KacperParaniuk/MonARCH-Electrical-Payload/hw/PIB/monarch_payload_interface_board_rev2/EXLA1V0402-R82-R/EXLA.stp

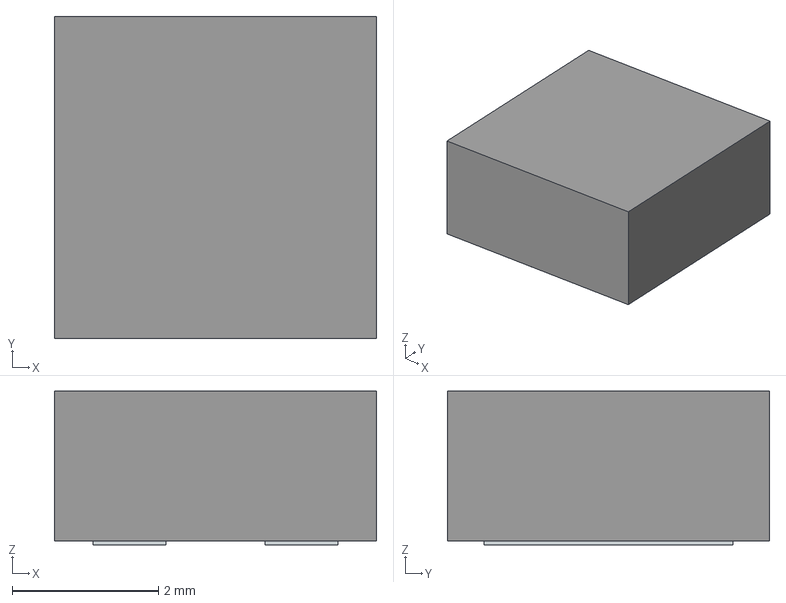
[picture p15: CAD file, 2026-03-08]
hw/PIB/monarch_payload_interface_board_rev2/EXLA1V0402-R82-R/EXLA.stp
4.40 x 4.40 x 2.10 mm
