KacperParaniuk/MonARCH-Electrical-Payload/hw/PIB/monarch_payload_interface_board_rev2/LIB_FZT600TA/FZT600TA/3D/FZT600TA.stp

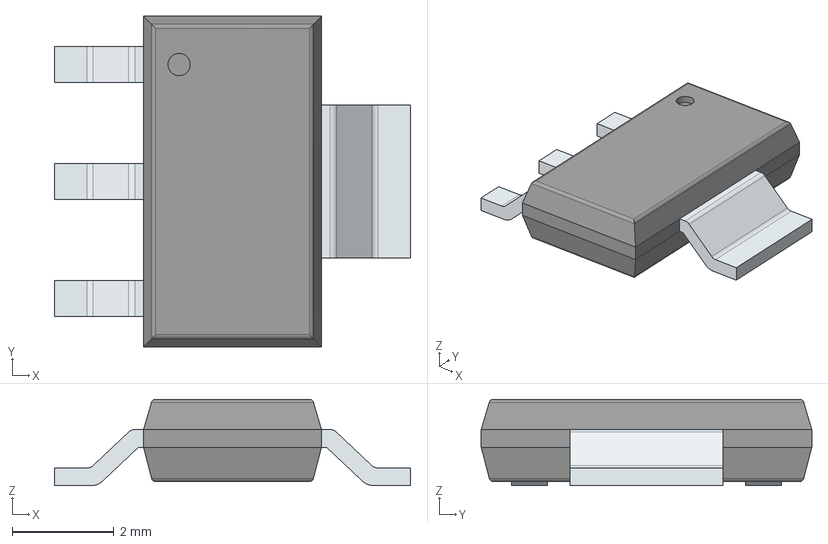
[picture p16: CAD file, 2026-02-22]
hw/PIB/monarch_payload_interface_board_rev2/LIB_FZT600TA/FZT600TA/3D/FZT600TA.stp
7.00 x 6.50 x 1.70 mm
PinsArrayL
FilletPinR
