KacperParaniuk/MonARCH-Electrical-Payload/hw/PIB/monarch_payload_interface_board_rev2/NZT7053/SOT-223_ONS.step

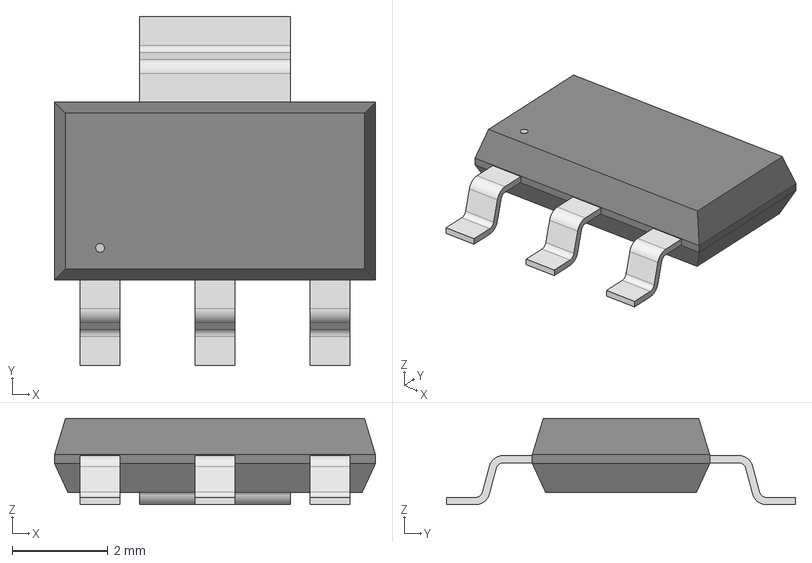
[picture p17: CAD file, 2026-02-22]
hw/PIB/monarch_payload_interface_board_rev2/NZT7053/SOT-223_ONS.step
6.71 x 7.29 x 1.81 mm
