KacperParaniuk/MonARCH-Electrical-Payload/hw/PIB/monarch_payload_interface_board_rev2/PIB_REV2.step

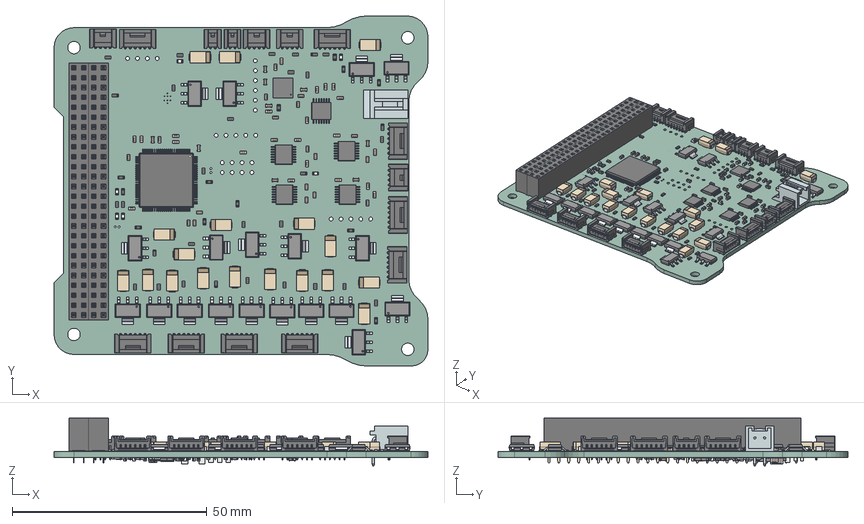
[picture p18: CAD file, 2026-07-30]
hw/PIB/monarch_payload_interface_board_rev2/PIB_REV2.step
96.0 x 89.9 x 12.3 mm
R_0603_1608Metric x 63
C_0603_1608Metric x 71
PinsArrayL x 19
FilletPinR x 19
LED_0603_1608Metric x 6
Body001 (Mirror #1) x 35
LQFP-100_14x14mm_P0.5mm
PinSocket_2x26_P2.54mm_Vertical x 2
534260210wbm000_01
WSK0612 x 3
C_1206_3216Metric x 2
C_0805_2012Metric x 5
BODY-QFN
PIN1-ID
monA6B6_PCB
