KacperParaniuk/MonARCH-Electrical-Payload/hw/PIB/monarch_payload_interface_board_rev2/S1J_13_F/SMA_DIO.step

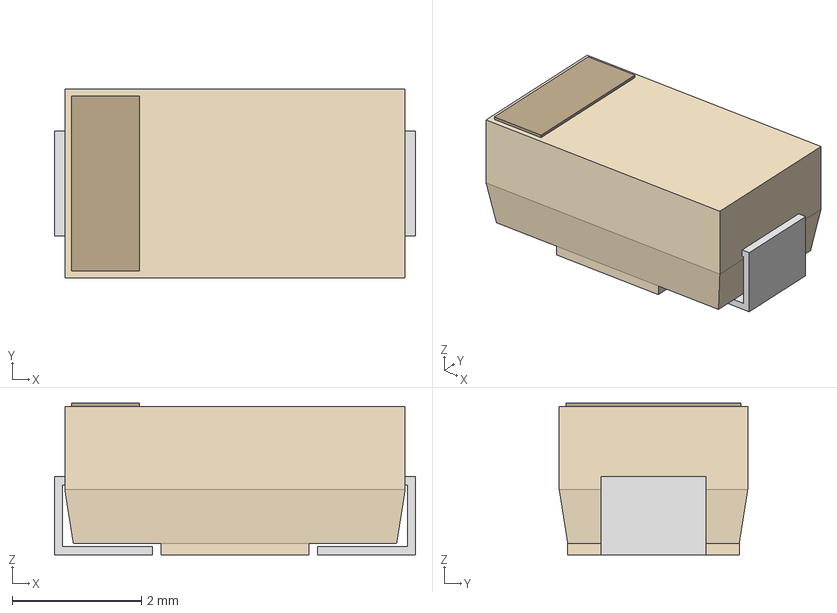
[picture p19: CAD file, 2026-02-22]
hw/PIB/monarch_payload_interface_board_rev2/S1J_13_F/SMA_DIO.step
5.59 x 2.92 x 2.35 mm
