KacperParaniuk/MonARCH-Electrical-Payload/hw/PIB/monarch_payload_interface_board_rev2/TPS61088QRHLRQ1/RHL0020A.stp

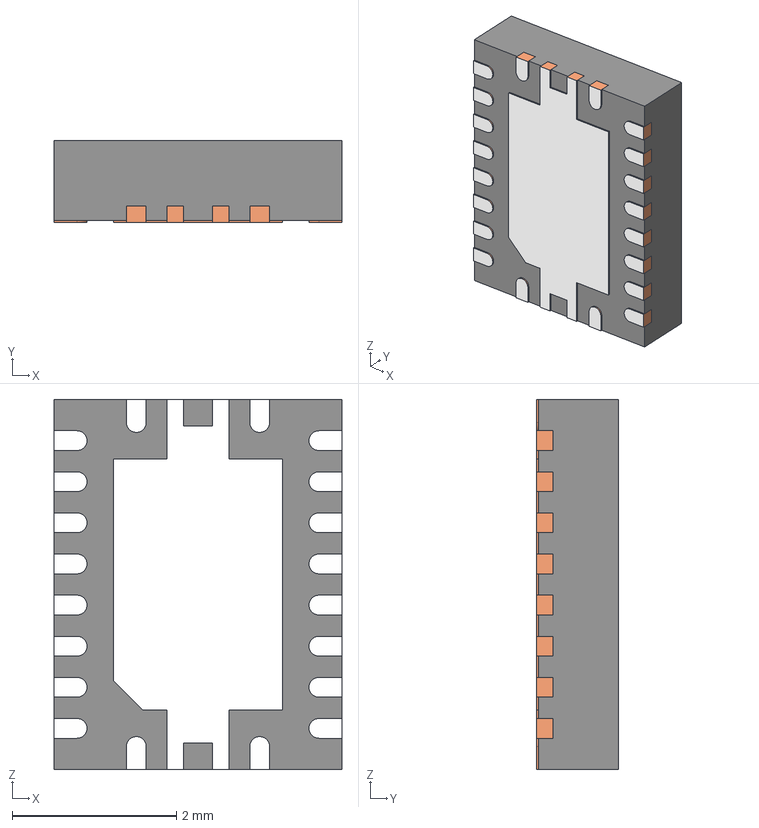
[picture p20: CAD file, 2026-02-22]
hw/PIB/monarch_payload_interface_board_rev2/TPS61088QRHLRQ1/RHL0020A.stp
3.50 x 1.00 x 4.50 mm
BODY-QFN
FRAME-RHL0020A
PIN1-ID
