KacperParaniuk/MonARCH-Electrical-Payload/hw/PIB/monarch_payload_interface_board_rev2/ul_WSK06121L000FEA/WSK0612.step

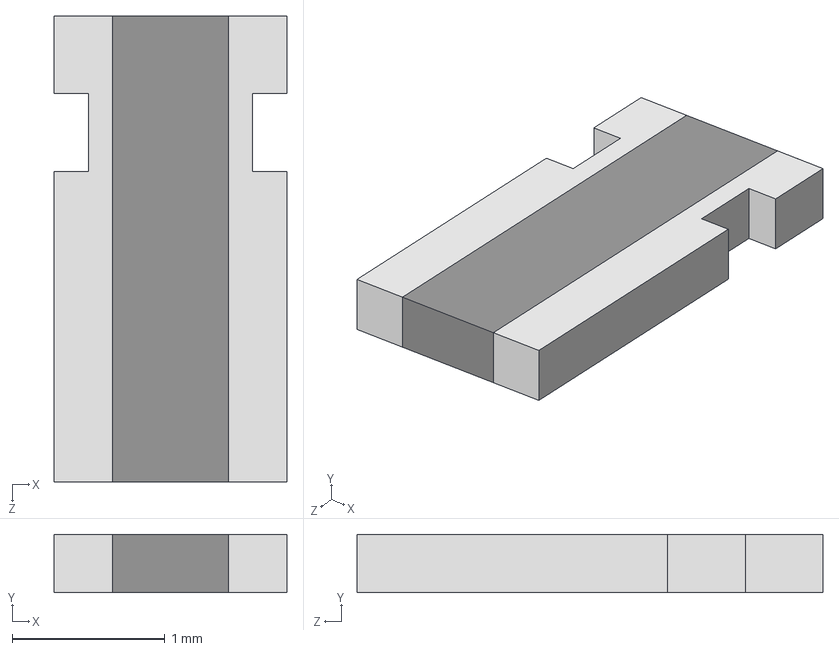
[picture p21: CAD file, 2026-03-08]
hw/PIB/monarch_payload_interface_board_rev2/ul_WSK06121L000FEA/WSK0612.step
1.52 x 0.381 x 3.05 mm
