KacperParaniuk/MonARCH-Electrical-Payload/sw/Main_PIB_Software/PIB_SOFTWARE/App/Inc/control_task.h

/*
 * contro_task.h
 *
 *  Created on: Mar 28, 2026
 *      Author: Kacper Paraniuk
 */

#ifndef INC_CONTROL_TASK_H_
#define INC_CONTROL_TASK_H_


#include "main.h"
#include <stdbool.h>
#include "max31856.h"


#define THRESHOLD_TEMP 60.0f // need to set correct threshold temperature value based on the readings we are getting.

void open_solenoid(GPIO_TypeDef* GPIO_port, uint16_t GPIO_Pin);
void close_solenoid(GPIO_TypeDef* GPIO_port, uint16_t GPIO_Pin);


int heat_catalyst(); // input a parameter into here to adjust the duty cycle of pwm signal. / the temperature




#endif /* INC_CONTROL_TASK_H_ */
