KacperParaniuk/MonARCH-Electrical-Payload/sw/Main_PIB_Software/PIB_SOFTWARE/BSP/Sensors/Inc/ad7124_sensor.h

/*
 * ad7124_sensor.h
 *
 *  Created on: Mar 17, 2026
 *      Author: Kacper Paraniuk
 */

#ifndef INC_AD7124_SENSOR_H_
#define INC_AD7124_SENSOR_H_


#include "ad7124.h"


extern struct ad7124_dev *ad7124;        // defined in main.c


#define CH_READ_PT0    0x0B
#define CH_READ_PT1    0x0C
#define CH_READ_PT2    0x0D
#define CH_READ_PT3    0x03
#define CH_READ_PT4    0x04
#define CH_READ_PT5    0x05
#define CH_READ_PT6    0x01
#define CH_READ_PT7    0x02


#define CH_READ_12VA_VB 0x00
#define CH_READ_12VA_VA 0x01
#define CH_READ_3V3_VB 0x02
#define CH_READ_3V3_VA 0x03
#define CH_READ_VBAT_VA 0x04
#define CH_READ_VBAT_VB 0x05
#define CH_READ_12VB_VA 0x06
#define CH_READ_12VB_VB 0x07


// Read a specific channel voltage
float ad7124_read_channel_voltage(struct ad7124_dev *device, uint8_t channel);
float ad7124_read_channel_current_pc104(struct ad7124_dev *device, uint8_t channel);




#endif /* INC_AD7124_SENSOR_H_ */
