KacperParaniuk/MonARCH-Electrical-Payload/sw/Main_PIB_Software/PIB_SOFTWARE/BSP/Sensors/Src/ad7124_console_app.c

/*!
 *****************************************************************************
  @file:  ad7124_console_app.c

  @brief: Implementation for the menu functions that handle the AD7124

  @details:
 -----------------------------------------------------------------------------
Copyright (c) 2019 Analog Devices, Inc.  All rights reserved.

Redistribution and use in source and binary forms, with or without modification,
are permitted provided that the following conditions are met:
  - Redistributions of source code must retain the above copyright notice,
    this list of conditions and the following disclaimer.
  - Redistributions in binary form must reproduce the above copyright notice,
    this list of conditions and the following disclaimer in the documentation
	and/or other materials provided with the distribution.
  - Modified versions of the software must be conspicuously marked as such.
  - This software is licensed solely and exclusively for use with processors/
    products manufactured by or for Analog Devices, Inc.
  - This software may not be combined or merged with other code in any manner
    that would cause the software to become subject to terms and conditions
	which differ from those listed here.
  - Neither the name of Analog Devices, Inc. nor the names of its contributors
    may be used to endorse or promote products derived from this software without
    specific prior written permission.
  - The use of this software may or may not infringe the patent rights of one
    or more patent holders.  This license does not release you from the
	requirement that you obtain separate licenses from these patent holders
	to use this software.

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
20180927-7CBSD SLA

*****************************************************************************/

/* includes */
#include <stdio.h>
#include <string.h>
#include <stdbool.h>

#include "platform_support.h"
#include "spi.h"
#include "error.h"

#include "ad7124.h"
#include "ad7124_regs.h"
#include "ad7124_support.h"
#include "ad7124_regs_configs.h"

#include "ad7124_console_app.h"


/*  defines */
#define AD7124_CHANNEL_COUNT 16

#define SHOW_ALL_CHANNELS     false
#define SHOW_ENABLED_CHANNELS  true

#define DISPLAY_DATA_TABULAR    0
#define DISPLAY_DATA_STREAM     1

#define MENU_ESCAPED			-1
#define MENU_CONTINUE           0
#define MENU_DONE               1

/* Private Variables */
/*
 * This is the 'live' AD7124 register map that is used by the driver
 * the other 'default' configs are used to populate this at init time
 */
static struct ad7124_st_reg ad7124_register_map_p[AD7124_REG_NO];

static struct ad7124_st_reg ad7124_register_map_v[AD7124_REG_NO];


// Pointer to the struct representing the AD7124 device // need to be able to utilize two ad7124 devices.

static struct ad7124_dev * pAd7124_dev = NULL; // p for pressure

// --------------

static struct ad7124_dev * vAd7124_dev = NULL; // v for voltage

uint32_t status;

// Last Sampled values for All ADC channels
static uint32_t channel_samples[AD7124_CHANNEL_COUNT] = {0};
// How many times a given channel is sampled in total for one sample run
static uint32_t channel_samples_count[AD7124_CHANNEL_COUNT] = {0};

// MAY USE THESE WHEN INTEGRATING DRIVER FUNCTIONS INTO MAIN.C

// Public Functions

/*!
 * @brief      Initialize the AD7124 device and the SPI port as required
 *
 * @details    This resets and then writes the default register map value to
 *  		   the device.  A call to init the SPI port is made, but may not
 *  		   actually do very much, depending on the platform
 */
int32_t ad7124_app_initialize(uint8_t configID, AD7124_CHIP chip)

// added param for cs -> CS = 0 = AD7124 POWER      |
				//       CS = 1 = AD7124 PRESSURE   | for measuring
{
	/*
	 * Copy one of the default/user configs to the live register memory map
	 * Requirement, not checked here, is that all the configs are the same size
	 *
	 */



	struct ad7124_st_reg *target_map = (chip == PRESSURE) ? ad7124_register_map_p : ad7124_register_map_v;

	switch(configID) {
		case AD7124_CONFIG_A:
		{
			memcpy(target_map, ad7124_regs_config_a, sizeof(struct ad7124_st_reg) * AD7124_REG_NO);
			break;
		}
		case AD7124_CONFIG_B:
		{
			memcpy(target_map, ad7124_regs_config_b, sizeof(struct ad7124_st_reg) * AD7124_REG_NO);
			break;
		}
		default:
			// Not a defined configID
			return(FAILURE);
	}




	if(chip==PRESSURE){

		// Used to create the ad7124 device (pressure)
	    struct	ad7124_init_param sAd7124_init = // ensure that when you are setting modfe
	  	{
	  		// spi_init_param type
	  		{
	  			2500000, 		// Max SPI Speed
	  			chip,				// Chip Select
				SPI_MODE_3,		// CPOL = 1, CPHA =1
				NULL
	  		},
	  		ad7124_register_map_p,

	  		10000				// Retry count for polling
	  	};

	    return(ad7124_setup(&pAd7124_dev, sAd7124_init));

	}

	else if(chip == VOLTAGE){

		// Used to create the ad7124 device (voltage)
	    struct	ad7124_init_param svAd7124_init = // ensure that when you are setting modfe
	  	{
	  		// spi_init_param type
	  		{
	  			2500000, 		// Max SPI Speed
	  			chip,				// Chip Select
				SPI_MODE_3,		// CPOL = 1, CPHA =1
				NULL

	  		},
	  		ad7124_register_map_v,

	  		10000				// Retry count for polling
	  	};


	    return(ad7124_setup(&vAd7124_dev, svAd7124_init));


	}

	return -20;

}


// ----- NOT USING MENU ------



// Private Functions

/*!
 * @brief      determines if the Escape key was pressed
 *
 * @details
 */
//static bool was_escape_key_pressed(void)
//{
//	char rxChar;
//	bool wasPressed = false;
//
//	// Check for Escape key pressed
//	if ((rxChar = getchar_nonblocking()) > 0) {
//		if (rxChar == ESCAPE_KEY_CODE) {
//			wasPressed = true;
//		}
//	}
//	return (wasPressed);
//}


/*!
 * @brief      reads and displays the status register on the AD7124
 *
 * @details
 */
void read_status_register(AD7124_CHIP chip)
{

    struct ad7124_dev *dev = (chip == PRESSURE) ? pAd7124_dev : vAd7124_dev;

	status = ad7124_read_register(dev, &dev->regs[AD7124_Status]);

	if (status < 0) {
	   printf("\r\nError Encountered reading Status register\r\n");
	} else {
	    uint32_t status_value = (uint32_t)dev->regs[AD7124_Status].value;
       printf("\r\nRead Status Register = 0x%02lx\r\n", status_value);
	}
}

static uint32_t error_value = 0;



void read_error_register(AD7124_CHIP chip){


    struct ad7124_dev *dev = (chip == PRESSURE) ? pAd7124_dev : vAd7124_dev;

	if (ad7124_read_register(dev, &dev->regs[AD7124_Error])==0){
		error_value = (uint32_t)dev->regs[AD7124_Error].value;
		if((error_value & AD7124_ERR_REG_ROM_CRC_ERR) != 0){
			printf("\r\n ROM Contents changed: CRC calculation fail: ROM error. \n");
		}
		if((error_value & AD7124_ERR_REG_MM_CRC_ERR) != 0){
			printf("\r\n CRC proves memory map changed: Memory map error. \n");
		}
		if((error_value & AD7124_ERR_REG_SPI_CRC_ERR) != 0){
			printf("\r\n CRC proves SPI read/write failed \n");
		}
		if((error_value & AD7124_ERR_REG_SPI_WRITE_ERR) != 0){
			printf("\r\n SPI write operation failed:  write to invalid addresses or write to read-only registers \n");
		}
		if((error_value & AD7124_ERR_REG_SPI_READ_ERR) != 0){
			printf("\r\n SPI read operation failed: attempt to read from invalid addresses \n");
		}
		if((error_value & AD7124_ERR_REG_SPI_SLCK_CNT_ERR) != 0){
			printf("\r\n The SCLK counter is enabled. All read and write operations to the ADC are multiples of eight bits: SCLK pulses used during a communication were not a multiple of eight \n");
		}
		if((error_value & AD7124_ERR_REG_SPI_IGNORE_ERR) != 0){
			printf("\r\n write operations are ignored from on chip registers ADC is busy and the write instruction has been ignored \n");
		}
		if((error_value & AD7124_ERR_REG_ALDO_PSM_ERR) != 0){
			printf("\r\n analog ldo: voltage being output from the analog LDO is outside specification. \n");
		}
		if((error_value & AD7124_ERR_REG_DLDO_PSM_ERR) != 0){
			printf("\r\n digital ldo: input to the test circuit is tied to DGND instead of the LDO output \n");
		}
		if((error_value & AD7124_ERR_REG_REF_DET_ERR) != 0){
			printf("\r\n External reference is an open circuit or has a value of less than 0.7 V. \n");
		}
		if((error_value & AD7124_ERR_REG_AINM_UV_ERR) != 0){
			printf("\r\n Undervoltage detection on AINM. \n");
		}
		if((error_value & AD7124_ERR_REG_AINM_OV_ERR) != 0){
			printf("\r\n Overvoltage detection on AINM. \n");
		}
		if((error_value & AD7124_ERR_REG_AINP_UV_ERR) != 0){
			printf("\r\n Undervoltage detection on AINP. \n");
		}
		if((error_value & AD7124_ERR_REG_AINP_OV_ERR) != 0){
			printf("\r\n Overvoltage detection on AINP \n");
		}
		if((error_value & AD7124_ERR_REG_ADC_SAT_ERR) != 0){
			printf("\r\n ADC saturation flag. This flag is set if the modulator is saturated during a conversion. \n");
		}
		if((error_value & AD7124_ERR_REG_ADC_CONV_ERR) != 0){
			printf("\r\n error occured during a conversion.");
		}
		if((error_value & AD7124_ERR_REG_ADC_CAL_ERR) != 0){
			printf("\r\n calibration error");
		}
		if((error_value & AD7124_ERR_REG_LDO_CAP_ERR) != 0){
			printf("\r\n decoupling capacitors required for the analog and digital LDOs are not connected to the AD7124-8.");
		}
	}
	else{
		printf("\r\n Error reading error register \n");
	}

}



/*!
 * @brief      displays the current sample value for a ADC channels
 *
 * @details
 *
 * @param showOnlyEnabledChannels  only channels that are enabled are displayed
 *
 */
static void dislay_channel_samples(bool showOnlyEnabledChannels, uint8_t console_mode, AD7124_CHIP chip)
{

    struct ad7124_dev *dev = (chip == PRESSURE) ? pAd7124_dev : vAd7124_dev;

	switch(console_mode) {
		case DISPLAY_DATA_TABULAR:
		{
			printf("\tCh\tValue\t\tCount\t\tVoltage\r\n");
			for (uint8_t i = 0; i < AD7124_CHANNEL_COUNT; i++) {
				// if showing all channels, or channel is enabled
				if ((showOnlyEnabledChannels == false) || (dev->regs[AD7124_Channel_0 + i].value & AD7124_CH_MAP_REG_CH_ENABLE) ) {
				   printf("\t%-2d\t%-10ld\t%ld\t\t% .6f\r\n",
							i, channel_samples[i], channel_samples_count[i],
							ad7124_convert_sample_to_voltage(dev, i, channel_samples[i]) );
				}
			}
			break;
		}
		case DISPLAY_DATA_STREAM:
		{
			// Output a CSV list of the sampled channels as voltages on a single line
			bool channel_printed = false;

			for (uint8_t i = 0; i < AD7124_CHANNEL_COUNT; i++) {
				// if showing all channels, or channel is enabled
				if ((showOnlyEnabledChannels == false) || (dev->regs[AD7124_Channel_0 + i].value & AD7124_CH_MAP_REG_CH_ENABLE) ) {
					/*
					 *  add the comma before we output the next channel but
					 *  only if at least one channel has been printed
					 */
				   if (channel_printed) {
					   printf(", ");
				   }
					printf("%.6f",
							ad7124_convert_sample_to_voltage(dev, i, channel_samples[i]) );
					channel_printed = true;
				}
			}
			printf("\r\n");
			break;
		}
		default:
		{
			// ASSERT(false);
		}
	}
}


float display_channel_sample(uint8_t channel, AD7124_CHIP chip){
	float value;

    struct ad7124_dev *dev = (chip == PRESSURE) ? pAd7124_dev : vAd7124_dev;

	// sample data into array
	menu_single_conversion(chip);


	// print channel
	value = ad7124_convert_sample_to_voltage(dev, channel, channel_samples[channel]);
	return value;
		//	printf("Channel %d: Voltage: %f ",channel, value);

}


/*!
 * @brief      resets the channelSampleCounts to zero
 *
 * @details
 */
static void clear_channel_samples(void)
{
    for (uint8_t i = 0; i < AD7124_CHANNEL_COUNT; i++) {
    	channel_samples[i] = 0;
    	channel_samples_count[i] = 0;
    }
}


/*!
 * @brief      Continuously acquires samples in Continuous Conversion mode
 *
 * @details   The ADC is run in continuous mode, and all samples are acquired
 *            and assigned to the channel they come from. Escape key an be used
 *            to exit the loop
 */
//
int32_t do_continuous_conversion(uint8_t display_mode,  AD7124_CHIP chip)
//
//
//  THOUGHTS ON CONTINOUS CONVERSION
//
//  IF I RUN THIS function in code it should just loop forever. And later I want to have a command that can toggle this on / off. Or just avoid function completely and only sample on command rather than continously
//
//
//
{
    struct ad7124_dev *dev = (chip == PRESSURE) ? pAd7124_dev : vAd7124_dev;

	int32_t error_code;
	int32_t sample_data;

	// Clear the ADC CTRL MODE bits, has the effect of selecting continuous mode
    dev->regs[AD7124_ADC_Control].value &= ~(AD7124_ADC_CTRL_REG_MODE(0xf));
	if ( (error_code = ad7124_write_register(dev, dev->regs[AD7124_ADC_Control]) ) < 0) {
		printf("Error (%ld) setting AD7124 Continuous conversion mode.\r\n", error_code);


//		adi_press_any_key_to_continue();
		return(MENU_CONTINUE);

	}

	clear_channel_samples();

	/*
	 *  If displaying data in stream form, want to output a channel header
	 */
	if (display_mode == DISPLAY_DATA_STREAM)
	{
		bool channel_printed = false;

		for (uint8_t i = 0; i < AD7124_CHANNEL_COUNT; i++) {
		   // if showing all channels, or channel is enabled
			if (dev->regs[AD7124_Channel_0 + i].value & AD7124_CH_MAP_REG_CH_ENABLE) {
				/*
				 *  add the comma before we output the next channel but
				 *  only if at least one channel has been printed
				 */
			   if (channel_printed) {
				   printf(", ");
			   }
				printf("%d", i);
			}
			channel_printed = true;
		}
		printf("\r\n");
	}

	uint8_t loop = 0;

	// Continuously read the channels, and store sample values
    while (true) { // was_escape_key_pressed() != true
    	toggle_activity_led(); // BLUE LED THAT WILL INDICATE PROGRESS or that the chip is running in continous mode.


    	if (display_mode == DISPLAY_DATA_TABULAR) {
//    		adi_clear_console();
    		printf("Running continuous conversion mode...\r\nPress Escape to stop\r\n\r\n"); //
    		//
    		//   THIS IS WHERE THE COMMAND WOULD GO FOR STOPPING CONTINOUS MODE. CURRENTLY IT'S JUST STUCK IN IT
    		//
    		//
    		//
    	}

		/*
		 *  this polls the status register READY/ bit to determine when conversion is done
		 *  this also ensures the STATUS register value is up to date and contains the
		 *  channel that was sampled as well.
		 *  Generally, no need to read STATUS separately, but for faster sampling
		 *  enabling the DATA_STATUS bit means that status is appended to ADC data read
		 *  so the channel being sampled is read back (and updated) as part of the same frame
		 */

    	if ( (error_code = ad7124_wait_for_conv_ready(dev, 10000)) < 0) {
    		printf("Error/Timeout waiting for conversion ready %ld\r\n", error_code);
    		continue;
    	}

    	if ( (error_code = ad7124_read_data(dev, &sample_data)) < 0) {
			printf("Error reading ADC Data (%ld).\r\n", error_code);
			continue;
		}

		/*
		 * No error, need to process the sample, what channel has been read? update that channelSample
		 */
		uint8_t channel_read = dev->regs[AD7124_Status].value & 0x0000000F;

		if (channel_read < AD7124_CHANNEL_COUNT) {
			channel_samples[channel_read] = sample_data;
			channel_samples_count[channel_read]++;
		} else {
			printf("Channel Read was %d, which is not < AD7124_CHANNEL_COUNT\r\n", channel_read);
		}

		dislay_channel_samples(SHOW_ENABLED_CHANNELS, display_mode, chip);

		HAL_Delay(1000); // One second delay see if it breaks

		if(loop==10){
			break; // now it will just break after 10 cycles
		}
		loop++;
		// if blank break


    }

    // All done, ADC put into standby mode
    dev->regs[AD7124_ADC_Control].value &= ~(AD7124_ADC_CTRL_REG_MODE(0xf));
    // 2 = sleep/standby mode
    dev->regs[AD7124_ADC_Control].value |= AD7124_ADC_CTRL_REG_MODE(2);

	if ( (error_code = ad7124_write_register(dev, dev->regs[AD7124_ADC_Control]) ) < 0) {
		printf("Error (%ld) setting AD7124 ADC into standby mode.\r\n", error_code);
//		adi_press_any_key_to_continue();
	}

	return(MENU_CONTINUE);
}


/*!
 * @brief      Samples all enabled channels and displays in tabular form
 *
 * @details
 */
//static int32_t menu_continuous_conversion_tabular(void)
//{
//	do_continuous_conversion(DISPLAY_DATA_TABULAR);
//
//	adi_clear_console();
//	printf("Continuous Conversion completed...\r\n\r\n");
//	dislay_channel_samples(SHOW_ALL_CHANNELS, DISPLAY_DATA_TABULAR);
//	adi_press_any_key_to_continue();
//
//	return(MENU_CONTINUE);
//}


/*!
 * @brief      Samples all enabled channels and displays on the console
 *
 * @details
 */
//static int32_t menu_continuous_conversion_stream(void)
//{
//	do_continuous_conversion(DISPLAY_DATA_STREAM);
//	printf("Continuous Conversion completed...\r\n\r\n");
//	adi_press_any_key_to_continue();
//	return(MENU_CONTINUE);
//}


/*!
 * @brief      Samples all enabled channels once in Single Conversion mode
 *
 * @details    This stores all channels that are enabled in a bitmask, and then
 *             runs the ADC in single conversion mode, which acquires one channel
 *             of data at a time. After capture, that channel is disabled, and
 *             single conversion run again, until no channels are enabled.
 *             The original enable state of each channel is then restored.
 */
int32_t menu_single_conversion(AD7124_CHIP chip)
{
	int32_t    error_code;
	uint16_t   channel_enable_mask = 0;
	uint8_t    channel_count = 0;
	int32_t    sample_data;

    struct ad7124_dev *dev = (chip == PRESSURE) ? pAd7124_dev : vAd7124_dev;


	// Need to store which channels are enabled in this config so it can be restored
	for (uint8_t i = 0; i < AD7124_CHANNEL_COUNT; i++) {
		if (dev->regs[AD7124_Channel_0 + i].value & AD7124_CH_MAP_REG_CH_ENABLE) {
			channel_enable_mask |= (1 << i);
			channel_count++;
		}
	}

	clear_channel_samples();
	//	adi_clear_console();
	printf("Running Single conversion mode...\r\nPress Escape to stop\r\n\r\n");

	// Clear the ADC CTRL MODE bits, selecting continuous mode
    dev->regs[AD7124_ADC_Control].value &= ~(AD7124_ADC_CTRL_REG_MODE(0xf));

	// read the channels, and store sample values
    for (uint8_t loopCount = 0; loopCount < channel_count ; loopCount++) {
    	toggle_activity_led(); // blue flicker twice = running single
    	HAL_Delay(200);
    	toggle_activity_led();

    	// 1 = single conversion mode
        dev->regs[AD7124_ADC_Control].value |= AD7124_ADC_CTRL_REG_MODE(1);

    	if ( (error_code = ad7124_write_register(dev, dev->regs[AD7124_ADC_Control]) ) < 0) {
    		printf("Error (%ld) setting AD7124 Single conversion mode.\r\n", error_code);
//    		adi_press_any_key_to_continue();
    		continue;
    	}

        /*
         *  this polls the status register READY/ bit to determine when conversion is done
         *  this also ensures the STATUS register value is up to date and contains the
         *  channel that was sampled as well. No need to read STATUS separately
         */
    	if ( (error_code = ad7124_wait_for_conv_ready(dev, 10000)) < 0) {
    		printf("Error/Timeout waiting for conversion ready %ld\r\n", error_code);
    		continue;
    	}

    	if ( (error_code = ad7124_read_data(dev, &sample_data)) < 0) {
			printf("Error reading ADC Data (%ld).\r\n", error_code);
			continue;
		}
    	/*
		 * No error, need to process the sample, what channel has been read? update that channelSample
		 */
		uint8_t channelRead = dev->regs[AD7124_Status].value & 0x0000000F;

		if (channelRead < AD7124_CHANNEL_COUNT) {
			channel_samples[channelRead] = sample_data;
			channel_samples_count[channelRead]++;

			/* also need to clear the channel enable bit so the next single conversion cycle will sample the next channel */
			dev->regs[AD7124_Channel_0 + channelRead].value &= ~AD7124_CH_MAP_REG_CH_ENABLE;
			if ( (error_code = ad7124_write_register(dev, dev->regs[AD7124_Channel_0 + channelRead]) ) < 0) {
				printf("Error (%ld) Clearing channel %d Enable bit.\r\n", error_code, channelRead);
//				adi_press_any_key_to_continue();
				continue;
			}
		} else {
			printf("Channel Read was %d, which is not < AD7124_CHANNEL_COUNT\r\n", channelRead);
		}
    }

    // All done, ADC put into standby mode
    dev->regs[AD7124_ADC_Control].value &= ~(AD7124_ADC_CTRL_REG_MODE(0xf));
    // 2 = sleep/standby mode
    dev->regs[AD7124_ADC_Control].value |= AD7124_ADC_CTRL_REG_MODE(2);

	// Need to restore the channels that were disabled during acquisition
	for (uint8_t i = 0; i < AD7124_CHANNEL_COUNT; i++) {
		if (channel_enable_mask & (1 << i)) {
			dev->regs[AD7124_Channel_0 + i].value |= AD7124_CH_MAP_REG_CH_ENABLE;
	    	if ( (error_code = ad7124_write_register(dev, dev->regs[AD7124_Channel_0 + i]) ) < 0) {
	    		printf("Error (%ld) Setting channel %d Enable bit.\r\r\n", error_code, i);
//	    		adi_press_any_key_to_continue();
	    		return(MENU_CONTINUE);
	    	}
		}
	}

	printf("Single Conversion completed...\r\n\r\n");
	dislay_channel_samples(SHOW_ENABLED_CHANNELS, DISPLAY_DATA_STREAM, chip);

//	adi_press_any_key_to_continue();
	return(MENU_CONTINUE);
}


/*!
 * @brief      menu item that reads the status register the AD7124
 *
 * @details
 */
//static int32_t menu_read_status(void)
//{
//	read_status_register();
//	adi_press_any_key_to_continue();
//	return(MENU_CONTINUE);
//}


/*!
 * @brief      reads the ID register on the AD7124
 *
 * @details
 */
//static int32_t menu_read_id(void)
//{
//	if (ad7124_read_register(pAd7124_dev, &ad7124_register_map[AD7124_ID]) < 0) {
//	   printf("\r\nError Encountered reading ID register\r\n");
//	} else {
//	   printf("\r\nRead ID Register = 0x%02lx\r\n",
//			   (uint32_t)ad7124_register_map[AD7124_ID].value );
//	}
//	adi_press_any_key_to_continue();
//	return(MENU_CONTINUE);
//}


/*!
 * @brief      Initialize the part with a specific configuration
 *
 * @details
 */


// IF WE WANTED TO REPROGRAM THE AD7124 MID CONFIG

//static void init_with_configuration(uint8_t configID)
//{
//	int32_t status = 0;
//
//	do {
//		if ((status = ad7124_remove(pAd7124_dev)) < 0) {
//			break;
//		}
//
//		if ((status = ad7124_app_initialize(configID)) < 0) {
//			break;
//		}
//	} while(0);
//
//	if (status < 0) {
//		printf("\r\n\r\n Error setting Configuration %c \r\n\r\n", (char)(configID + 'A'));
//	} else {
//		printf("\r\n\r\n Configuration %c Set\r\n\r\n", (char)(configID + 'A'));
//	}
//	adi_press_any_key_to_continue();
//}


/*
 * @brief      Sends a reset command on the SPI to reset the AD7124
 *
 * @details
 */

int32_t ad7124_reset_function(AD7124_CHIP chip)
{


    struct ad7124_dev *dev = (chip == PRESSURE) ? pAd7124_dev : vAd7124_dev;

	if (ad7124_reset(dev)  < 0)
	{
		printf("\r\n\r\n Error performing Reset\r\n\r\n");
	} else
	{
		// Need to set the live register map to defaults as well
		memcpy(dev->regs, ad7124_regs, sizeof(dev->regs) * AD7124_REG_NO);
		printf("\r\n\r\n Reset Complete\r\n\r\n");
	}

//	adi_press_any_key_to_continue();
	return(MENU_CONTINUE);
}




int32_t ad7124_read_device_id(AD7124_CHIP chip){


    struct ad7124_dev *dev = (chip == PRESSURE) ? pAd7124_dev : vAd7124_dev;

	status = ad7124_read_register(dev, &dev->regs[AD7124_ID]);

	  if (status < 0) {
	  	   printf("\r\nError Encountered reading ID register\r\n");
	  }
	  else {
	  	   printf("\r\nRead ID Register = 0x%02lx\r\n",
	  	   (uint32_t)dev->regs[AD7124_ID].value);

	  	   return (uint32_t)dev->regs[AD7124_ID].value;
	  }

	  return -1;


}


float ad7124_read_channel_current_pc104(uint8_t channel){
	
	// read the channel voltage from the ad7124
	float voltage = display_channel_sample(channel, VOLTAGE);

	// convert the voltage to current using the formula I = (Vout - 0.5) / 0.16
	float current = (voltage) / 100000; // 100k resistor in series with all volt voltage dividers 

	return current;

}




/*!
 * @brief      Reset and set the ad7124 with configuration A
 *
 * @details
 */
//static int32_t menu_reset_to_configuration_a(void)
//{
//	init_with_configuration(AD7124_CONFIG_A);
//	return(MENU_CONTINUE);
//}


/*!
 * @brief      Reset and the ad7124 with configuration B
 *
 * @details
 */
//static int32_t menu_reset_to_configuration_b(void)
//{
//	init_with_configuration(AD7124_CONFIG_B);
//	return(MENU_CONTINUE);
//}


/*
 * Definition of the Sampling Menu Items and menu itself
 */
//static console_menu_item acquisition_menu_items[] = {
//		{"Single Conversion Mode",	                 	'S', menu_single_conversion},
//	    {"Continuous Conversion Mode - Table View",	    'T', menu_continuous_conversion_tabular},
//		{"Continuous Conversion Mode - Stream Data",	'C', menu_continuous_conversion_stream},
//};
//
//static console_menu acquisition_menu = {
//    "Data Acquisition Menu",
//	acquisition_menu_items,
//	ARRAY_SIZE(acquisition_menu_items),
//	true
//};


/*!
 * @brief      displays and handles the Sample Channel menu
 *
 * @details
 */
//static int32_t menu_sample_channels(void)
//{
//	return(adi_do_console_menu(&acquisition_menu));
//}


/*
 * Definition of the Main Menu Items and menu itself
// */
//console_menu_item main_menu_items[] = {
//	{"Reset to Default Configuration",	'R', menu_reset},
//	{"Reset to Configuration A",		'A', menu_reset_to_configuration_a},
//    {"Reset to Configuration B",		'B', menu_reset_to_configuration_b},
//	{"", 								'\00', NULL},
//	{"Read ID Register",				'I', menu_read_id},
//	{"Read Status Register",			'T', menu_read_status},
//	{"", 								'\00', NULL},
//    {"Sample Channels...",				'S', menu_sample_channels},
//};
//
//console_menu ad7124_main_menu = {
//    "AD7124 Main Menu",
//    main_menu_items,
//	ARRAY_SIZE(main_menu_items),
//	false
//};
