KacperParaniuk/MonARCH-Electrical-Payload/sw/Main_PIB_Software/PIB_SOFTWARE/Core/Inc/systems.h

#include "flags.h"
#include "fsm_states.h"
#include "data_log.h"

typedef struct {
    // main struct that will be passed into everything
    enum FSMState fsm_state;  // current sys fsm state
    struct system_flags sys_flags;   // sys flags for allowing and rejecting commands 
    struct error_flags err_flags;  // error flags polled throughout the system 
    struct Data_Log data_log; // all of payload data 

} Payload_System; 
