KacperParaniuk/MonARCH-Electrical-Payload/sw/Main_PIB_Software/PIB_SOFTWARE/Core/Inc/fsm_config.h

// Will input various configuration parameters for the FSM module. This file is used to define the configuration settings that will be used by the FSM (Finite State Machine) implementation in the project. The configuration parameters may include state definitions, transition rules, event handling mechanisms, and other relevant settings that dictate how the FSM operates within the application.
