KacperParaniuk/MonARCH-Electrical-Payload/sw/Random-Test-Software/Test_PIB_Software/UART_Test/CM7/Core/Src/main.c

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
/* Includes ------------------------------------------------------------------*/
#include "main.h"

/* USER CODE BEGIN PD */

/* DUAL_CORE_BOOT_SYNC_SEQUENCE: Define for dual core boot synchronization    */
/*                             demonstration code based on hardware semaphore */
/* This define is present in both CM7/CM4 projects                            */
/* To comment when developping/debugging on a single core                     */
#define DUAL_CORE_BOOT_SYNC_SEQUENCE

#if defined(DUAL_CORE_BOOT_SYNC_SEQUENCE)
#ifndef HSEM_ID_0
#define HSEM_ID_0 (0U) /* HW semaphore 0*/
#endif
#endif /* DUAL_CORE_BOOT_SYNC_SEQUENCE */

/* USER CODE END PD */


UART_HandleTypeDef hlpuart1;

void SystemClock_Config(void);
static void MPU_Config(void);
static void MX_GPIO_Init(void);
static void MX_LPUART1_UART_Init(void);
/**
  * @brief  The application entry point.
  * @retval int
  */
int main(void)
{

/* USER CODE BEGIN Boot_Mode_Sequence_0 */
#if defined(DUAL_CORE_BOOT_SYNC_SEQUENCE)
  int32_t timeout;
#endif /* DUAL_CORE_BOOT_SYNC_SEQUENCE */
/* USER CODE END Boot_Mode_Sequence_0 */

  /* MPU Configuration--------------------------------------------------------*/
  MPU_Config();

/* USER CODE BEGIN Boot_Mode_Sequence_1 */
#if defined(DUAL_CORE_BOOT_SYNC_SEQUENCE)
  /* Wait until CPU2 boots and enters in stop mode or timeout*/
  timeout = 0xFFFF;
  while((__HAL_RCC_GET_FLAG(RCC_FLAG_D2CKRDY) != RESET) && (timeout-- > 0));
  if ( timeout < 0 )
  {
  Error_Handler();
  }
#endif /* DUAL_CORE_BOOT_SYNC_SEQUENCE */
/* USER CODE END Boot_Mode_Sequence_1 */
  /* MCU Configuration--------------------------------------------------------*/

  /* Reset of all peripherals, Initializes the Flash interface and the Systick. */
  HAL_Init();

  /* Configure the system clock */
  SystemClock_Config();
/* USER CODE BEGIN Boot_Mode_Sequence_2 */
#if defined(DUAL_CORE_BOOT_SYNC_SEQUENCE)
/* When system initialization is finished, Cortex-M7 will release Cortex-M4 by means of
HSEM notification */
/*HW semaphore Clock enable*/
__HAL_RCC_HSEM_CLK_ENABLE();
/*Take HSEM */
HAL_HSEM_FastTake(HSEM_ID_0);
/*Release HSEM in order to notify the CPU2(CM4)*/
HAL_HSEM_Release(HSEM_ID_0,0);
/* wait until CPU2 wakes up from stop mode */
timeout = 0xFFFF;
while((__HAL_RCC_GET_FLAG(RCC_FLAG_D2CKRDY) == RESET) && (timeout-- > 0));
if ( timeout < 0 )
{
Error_Handler();
}
#endif /* DUAL_CORE_BOOT_SYNC_SEQUENCE */
/* USER CODE END Boot_Mode_Sequence_2 */

  /* Initialize all configured peripherals */
  MX_GPIO_Init();
  MX_LPUART1_UART_Init();
  /* USER CODE BEGIN 2 */

  // Enable GPIO clock
//   __HAL_RCC_GPIOA_CLK_ENABLE();

   // Configure GPIO pin
   GPIO_InitTypeDef GPIO_InitStruct = {0};
   GPIO_InitStruct.Pin = GPIO_PIN_8;           // Change pin as needed
   GPIO_InitStruct.Mode = GPIO_MODE_OUTPUT_PP;
   GPIO_InitStruct.Pull = GPIO_NOPULL;
   GPIO_InitStruct.Speed = GPIO_SPEED_FREQ_LOW;
   HAL_GPIO_Init(GPIOB, &GPIO_InitStruct);     // Change port as needed

  /* USER CODE END 2 */

  /* Infinite loop */
  /* USER CODE BEGIN WHILE */
  while (1)
  {
//
//	  HAL_GPIO_TogglePin(GPIOB,GPIO_PIN_14); // RED LED TOGGLE
//	  HAL_Delay(500);
////
//	  HAL_UART_Transmit_IT(&hlpuart1, tx_buff, 10);
//	  HAL_Delay(10000);

	  // Turn LED ON
	  HAL_GPIO_WritePin(GPIOB, GPIO_PIN_8, GPIO_PIN_SET);
	  HAL_Delay(500);

	  // Turn LED OFF
	  HAL_GPIO_WritePin(GPIOB, GPIO_PIN_8, GPIO_PIN_RESET);
	  HAL_Delay(500);

	  HAL_GPIO_WritePin(val, GPIO_Pin, PinState)








	  // to be implemented -> Test Code for UART interrupt from OBC

//
//	  while(uart receive){













//
//
//	  }













    /* USER CODE END WHILE */

    /* USER CODE BEGIN 3 */
  }
  /* USER CODE END 3 */
}

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
 /* MPU Configuration */

void MPU_Config(void)
{
  MPU_Region_InitTypeDef MPU_InitStruct = {0};

  /* Disables the MPU */
  HAL_MPU_Disable();

  /** Initializes and configures the Region and the memory to be protected
  */
  MPU_InitStruct.Enable = MPU_REGION_ENABLE;
  MPU_InitStruct.Number = MPU_REGION_NUMBER0;
  MPU_InitStruct.BaseAddress = 0x0;
  MPU_InitStruct.Size = MPU_REGION_SIZE_4GB;
  MPU_InitStruct.SubRegionDisable = 0x87;
  MPU_InitStruct.TypeExtField = MPU_TEX_LEVEL0;
  MPU_InitStruct.AccessPermission = MPU_REGION_NO_ACCESS;
  MPU_InitStruct.DisableExec = MPU_INSTRUCTION_ACCESS_DISABLE;
  MPU_InitStruct.IsShareable = MPU_ACCESS_SHAREABLE;
  MPU_InitStruct.IsCacheable = MPU_ACCESS_NOT_CACHEABLE;
  MPU_InitStruct.IsBufferable = MPU_ACCESS_NOT_BUFFERABLE;

  HAL_MPU_ConfigRegion(&MPU_InitStruct);
  /* Enables the MPU */
  HAL_MPU_Enable(MPU_PRIVILEGED_DEFAULT);

}

/**
  * @brief  This function is executed in case of error occurrence.
  * @retval None
  */
void Error_Handler(void)
{
  /* USER CODE BEGIN Error_Handler_Debug */
  /* User can add his own implementation to report the HAL error return state */
  __disable_irq();
  while (1)
  {
  }
  /* USER CODE END Error_Handler_Debug */
}
#ifdef USE_FULL_ASSERT
/**
  * @brief  Reports the name of the source file and the source line number
  *         where the assert_param error has occurred.
  * @param  file: pointer to the source file name
  * @param  line: assert_param error line source number
  * @retval None
  */
void assert_failed(uint8_t *file, uint32_t line)
{
  /* USER CODE BEGIN 6 */
  /* User can add his own implementation to report the file name and line number,
     ex: printf("Wrong parameters value: file %s on line %d\r\n", file, line) */
  /* USER CODE END 6 */
}
#endif /* USE_FULL_ASSERT */
