KacperParaniuk/MonARCH-Electrical-Payload/sw/Random-Test-Software/Test_PIB_Software/UART_Test/CM7/BSP/Inc/pins.h

/*
 * pins.h
 *
 *  Created on: Feb 24, 2026
 *      Author: Kacper Paraniuk
 */

#ifndef INC_PINS_H_
#define INC_PINS_H_


#include "main.h" // get pin assignments <- Be able to include pins.h and get everything.

// Aliases

// define constants.

// Board Level Constants:








#endif /* INC_PINS_H_ */
